George5683/GatorGrid-Mesh/docs/html/ap__one_8cpp__incl.png

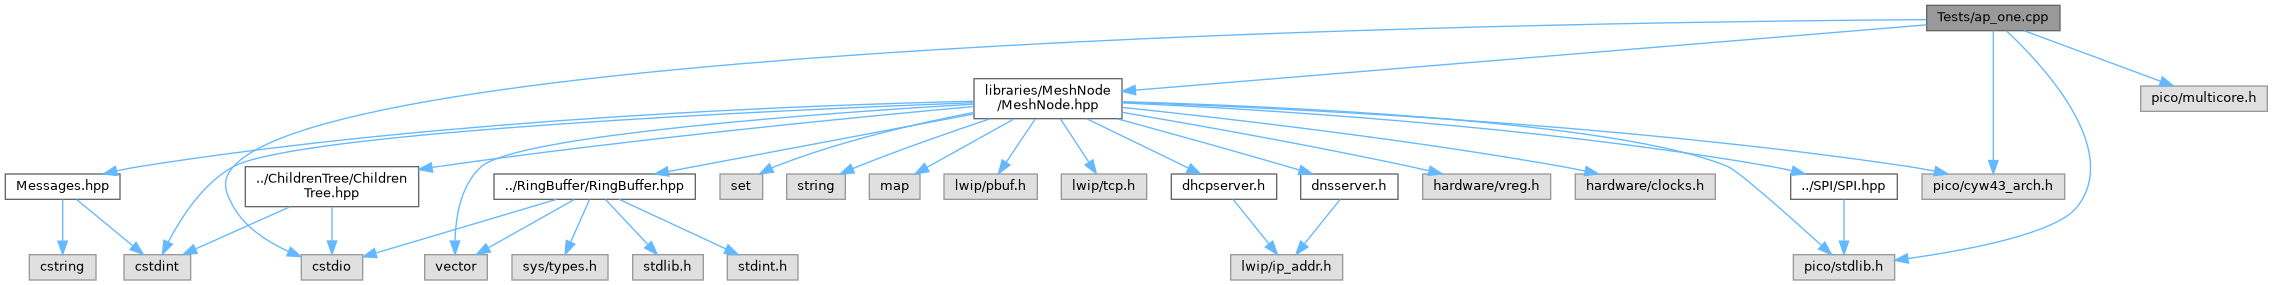
docs/html/ap__one_8cpp__incl.png
