George5683/GatorGrid-Mesh/docs/html/ChildrenTree_8cpp__incl.png

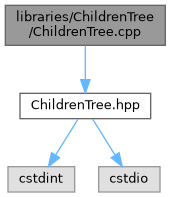
docs/html/ChildrenTree_8cpp__incl.png
