George5683/GatorGrid-Mesh/docs/html/ChildrenTree_8hpp__dep__incl.png

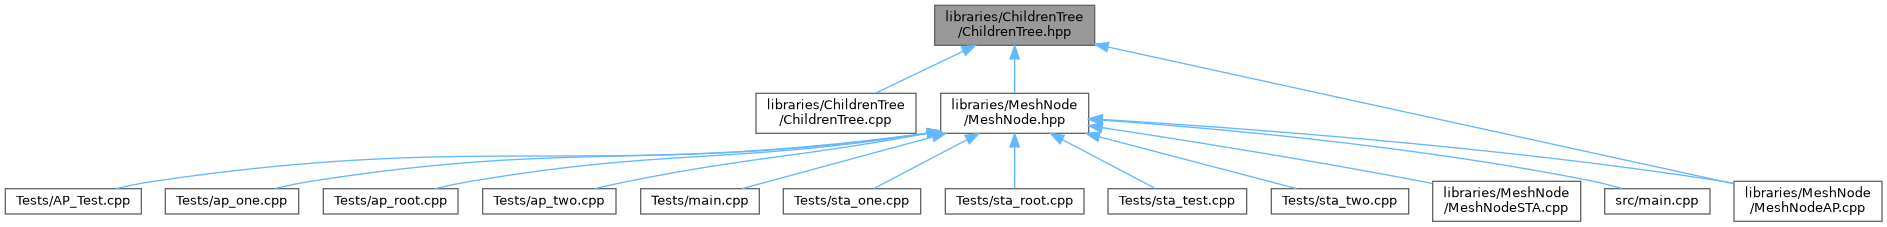
docs/html/ChildrenTree_8hpp__dep__incl.png
