George5683/GatorGrid-Mesh/docs/html/classAPNode__coll__graph.png

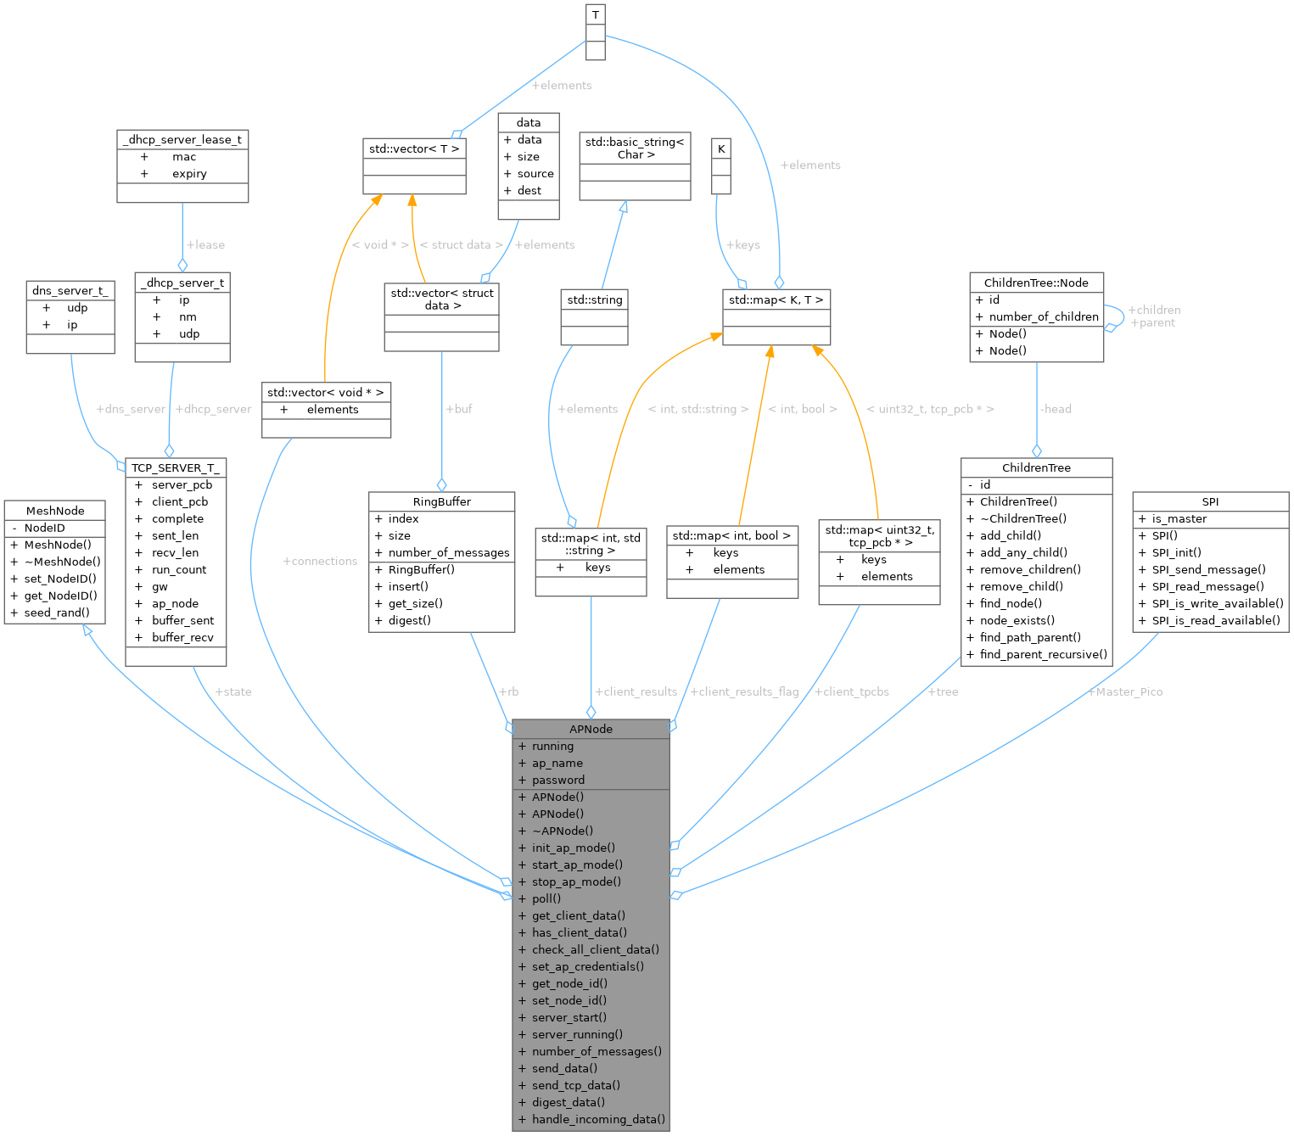
docs/html/classAPNode__coll__graph.png
