George5683/GatorGrid-Mesh/docs/html/classChildrenTree__coll__graph.png

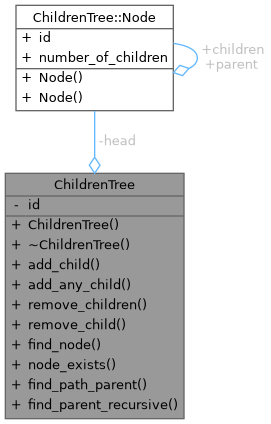
docs/html/classChildrenTree__coll__graph.png
