George5683/GatorGrid-Mesh/docs/html/classMeshNode__coll__graph.png

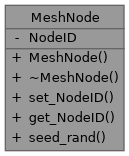
docs/html/classMeshNode__coll__graph.png
