George5683/GatorGrid-Mesh/docs/html/classMeshNode__inherit__graph.png

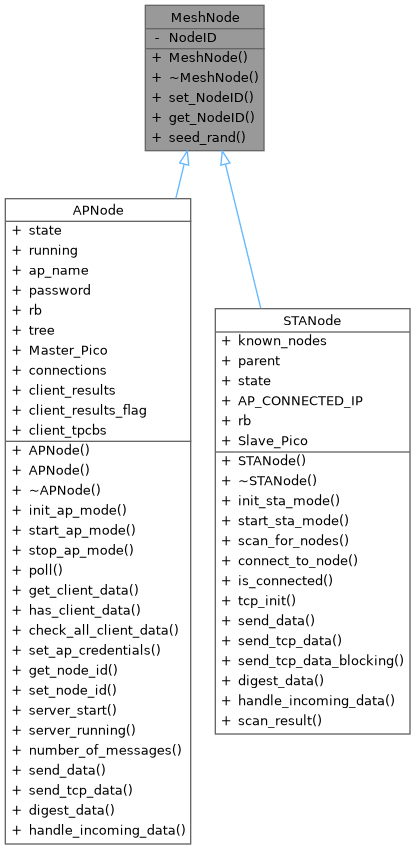
docs/html/classMeshNode__inherit__graph.png
