George5683/GatorGrid-Mesh/docs/html/classRingBuffer__coll__graph.png

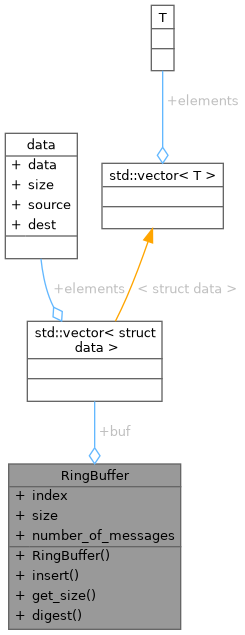
docs/html/classRingBuffer__coll__graph.png
