George5683/GatorGrid-Mesh/docs/html/classSPI__coll__graph.png

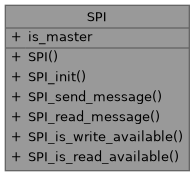
docs/html/classSPI__coll__graph.png
