George5683/GatorGrid-Mesh/docs/html/classSTANode__coll__graph.png

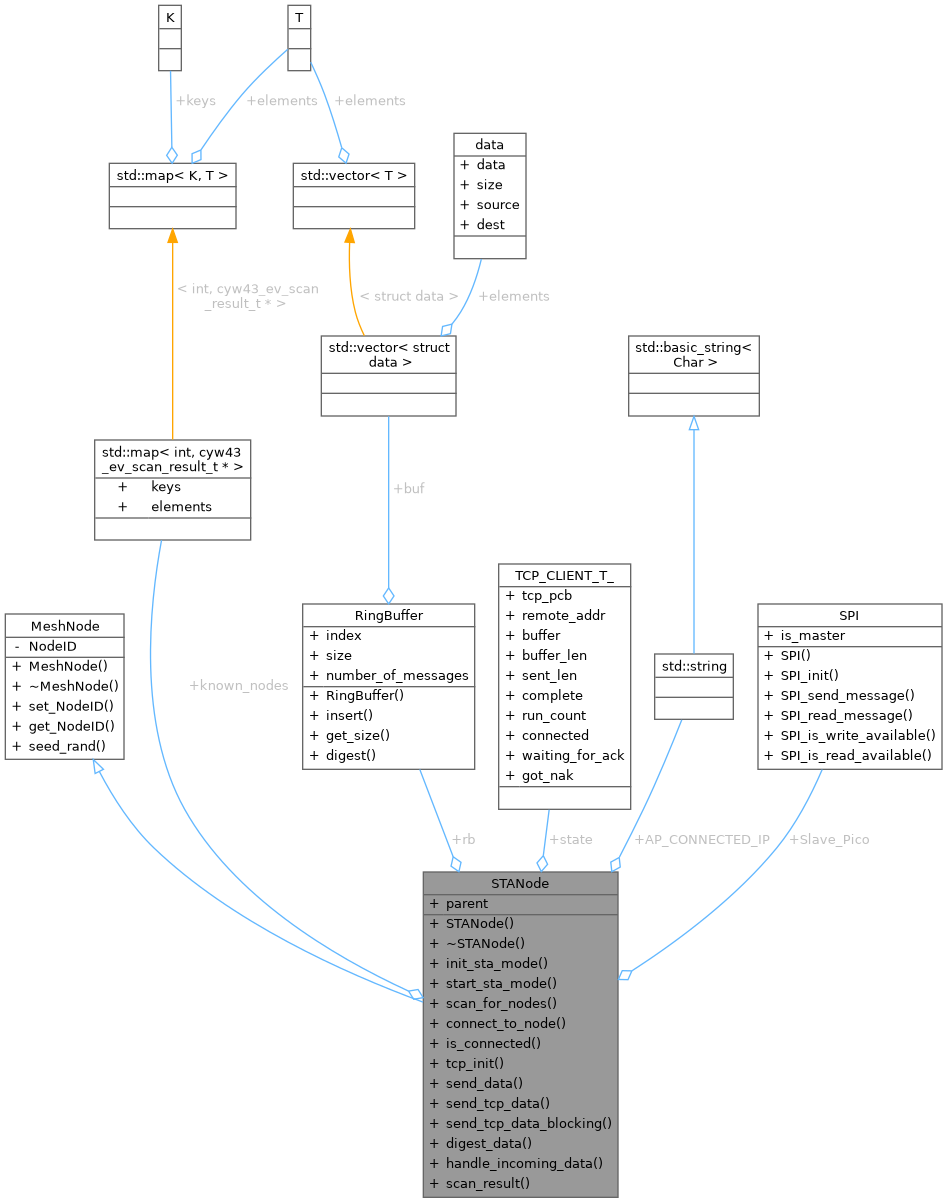
docs/html/classSTANode__coll__graph.png
