George5683/GatorGrid-Mesh/docs/html/classSTANode__inherit__graph.png

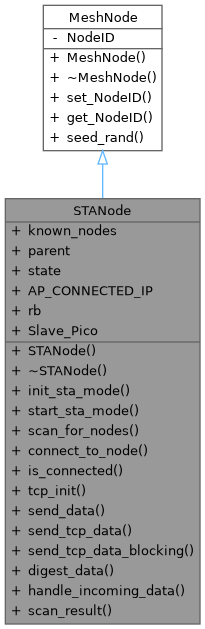
docs/html/classSTANode__inherit__graph.png
