George5683/GatorGrid-Mesh/docs/html/classTCP__ACK__MESSAGE__coll__graph.png

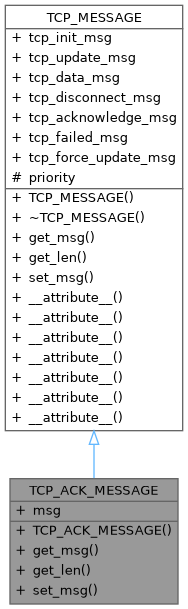
docs/html/classTCP__ACK__MESSAGE__coll__graph.png
