George5683/GatorGrid-Mesh/docs/html/classTCP__DATA__MSG__coll__graph.png

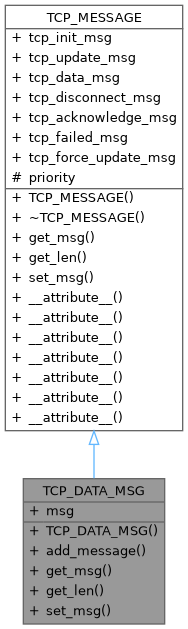
docs/html/classTCP__DATA__MSG__coll__graph.png
