George5683/GatorGrid-Mesh/docs/html/classTCP__MESSAGE__coll__graph.png

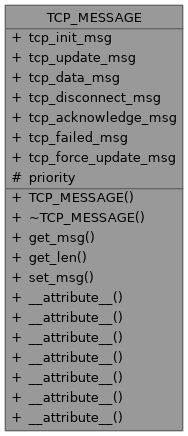
docs/html/classTCP__MESSAGE__coll__graph.png
