George5683/GatorGrid-Mesh/docs/html/classTCP__MESSAGE__inherit__graph.png

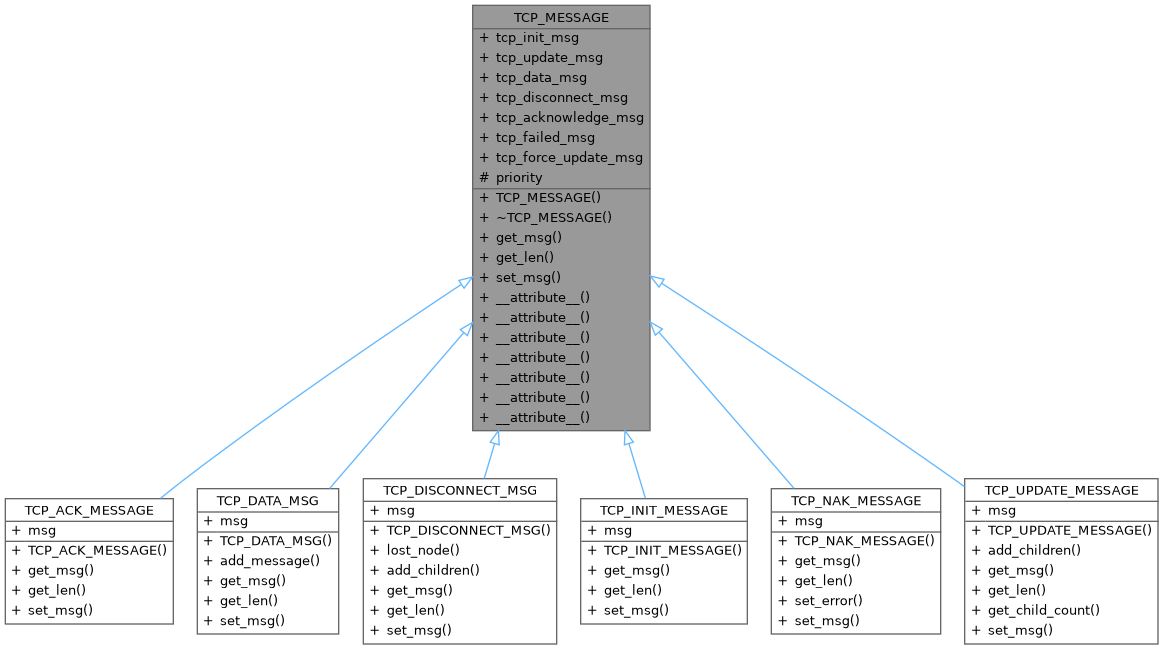
docs/html/classTCP__MESSAGE__inherit__graph.png
