George5683/GatorGrid-Mesh/docs/html/classTCP__NAK__MESSAGE__coll__graph.png

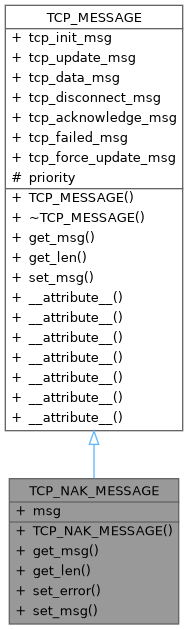
docs/html/classTCP__NAK__MESSAGE__coll__graph.png
