George5683/GatorGrid-Mesh/docs/html/dhcpserver_8c__incl.png

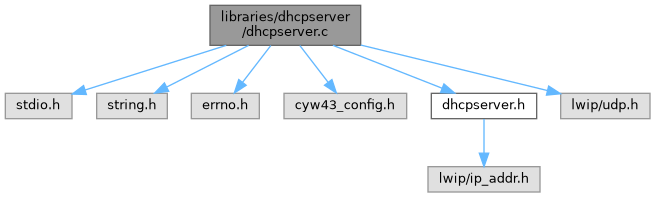
docs/html/dhcpserver_8c__incl.png
