George5683/GatorGrid-Mesh/docs/html/dhcpserver_8h__dep__incl.png

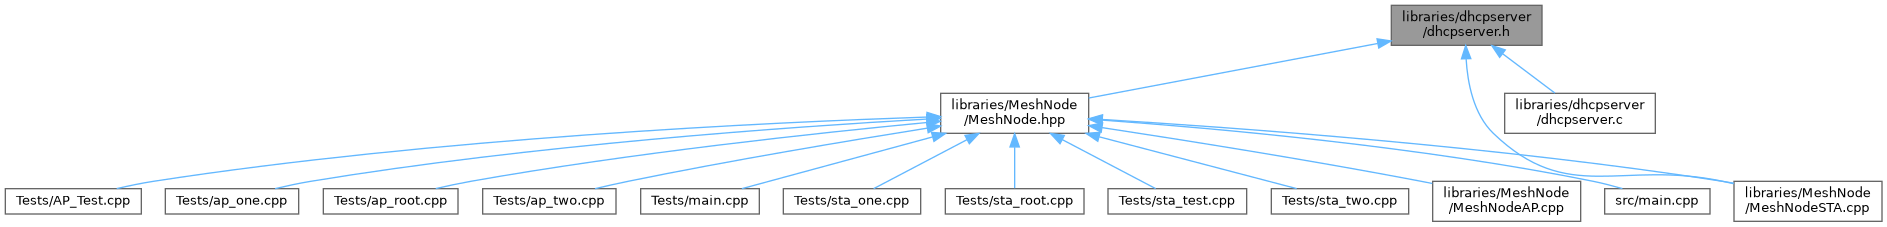
docs/html/dhcpserver_8h__dep__incl.png
