George5683/GatorGrid-Mesh/docs/html/dir_33c78a012c8d08979f57a54a07694c46_dep.png

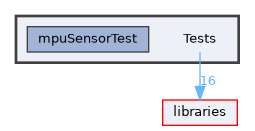
docs/html/dir_33c78a012c8d08979f57a54a07694c46_dep.png
