George5683/GatorGrid-Mesh/docs/html/dir_bc0718b08fb2015b8e59c47b2805f60c_dep.png

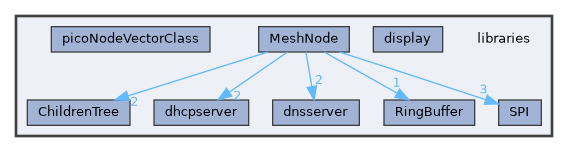
docs/html/dir_bc0718b08fb2015b8e59c47b2805f60c_dep.png
