George5683/GatorGrid-Mesh/docs/html/dir_e2eb97f4390ebb17dad96716298a140a_dep.png

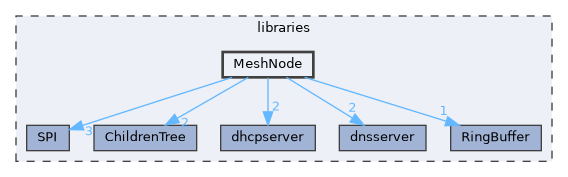
docs/html/dir_e2eb97f4390ebb17dad96716298a140a_dep.png
