George5683/GatorGrid-Mesh/docs/html/dnsserver_8c__incl.png

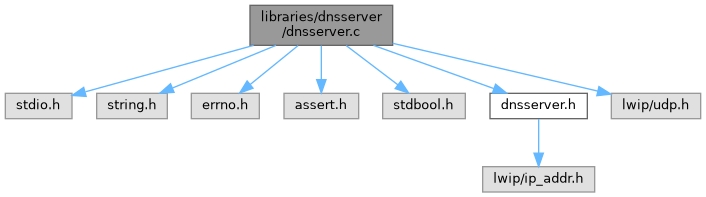
docs/html/dnsserver_8c__incl.png
