George5683/GatorGrid-Mesh/docs/html/dnsserver_8h__incl.png

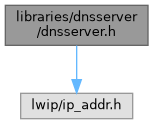
docs/html/dnsserver_8h__incl.png
