George5683/GatorGrid-Mesh/docs/html/inherit_graph_15.png

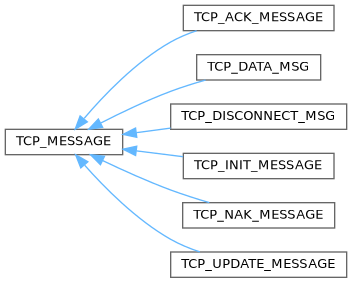
docs/html/inherit_graph_15.png
