George5683/GatorGrid-Mesh/docs/html/MeshNode_8hpp__incl.png

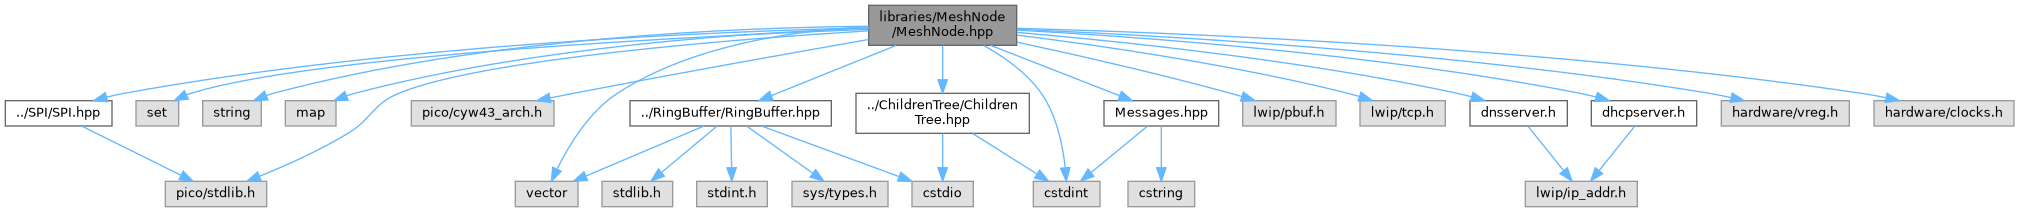
docs/html/MeshNode_8hpp__incl.png
