George5683/GatorGrid-Mesh/docs/html/MeshNodeAP_8cpp__incl.png

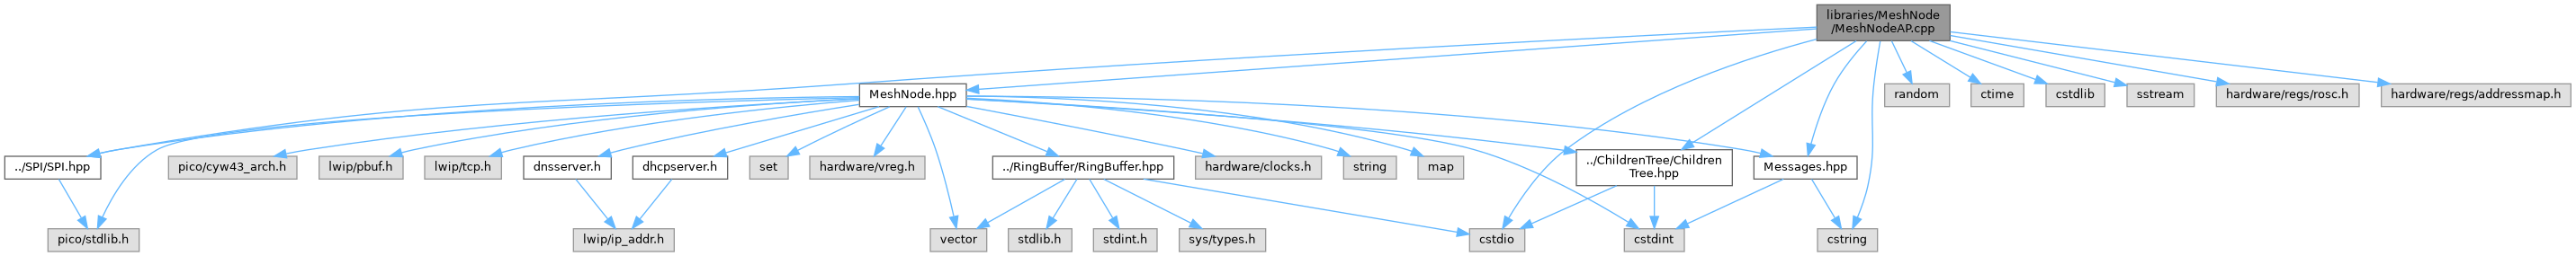
docs/html/MeshNodeAP_8cpp__incl.png
