George5683/GatorGrid-Mesh/docs/html/MeshNodeSTA_8cpp__incl.png

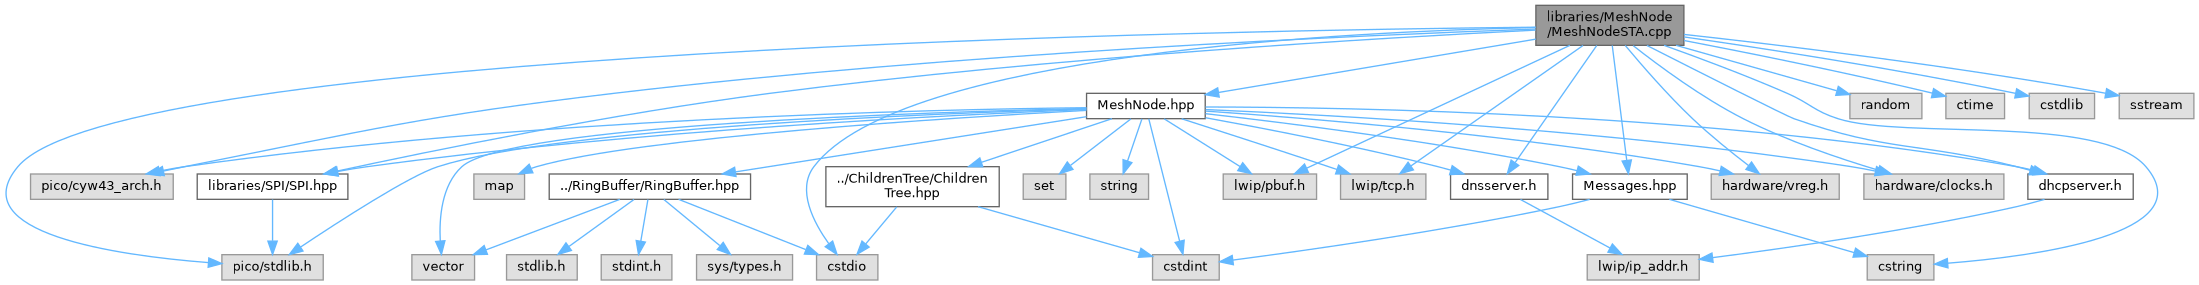
docs/html/MeshNodeSTA_8cpp__incl.png
