George5683/GatorGrid-Mesh/docs/html/Messages_8cpp__incl.png

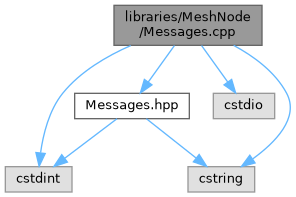
docs/html/Messages_8cpp__incl.png
