George5683/GatorGrid-Mesh/docs/html/Messages_8hpp__incl.png

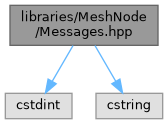
docs/html/Messages_8hpp__incl.png
