George5683/GatorGrid-Mesh/docs/html/RingBuffer_8cpp__incl.png

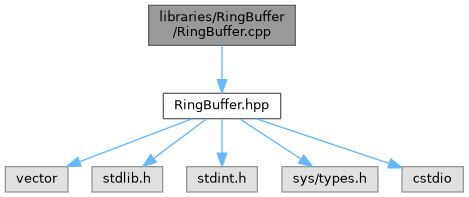
docs/html/RingBuffer_8cpp__incl.png
