George5683/GatorGrid-Mesh/docs/html/RingBuffer_8hpp__incl.png

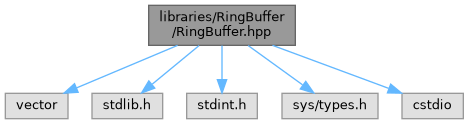
docs/html/RingBuffer_8hpp__incl.png
