George5683/GatorGrid-Mesh/docs/html/SPI_8cpp__incl.png

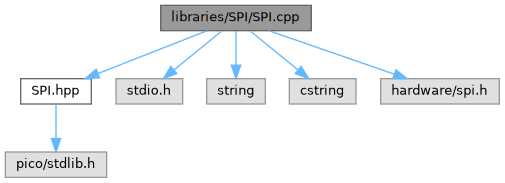
docs/html/SPI_8cpp__incl.png
