George5683/GatorGrid-Mesh/docs/html/SPI_8hpp__dep__incl.png

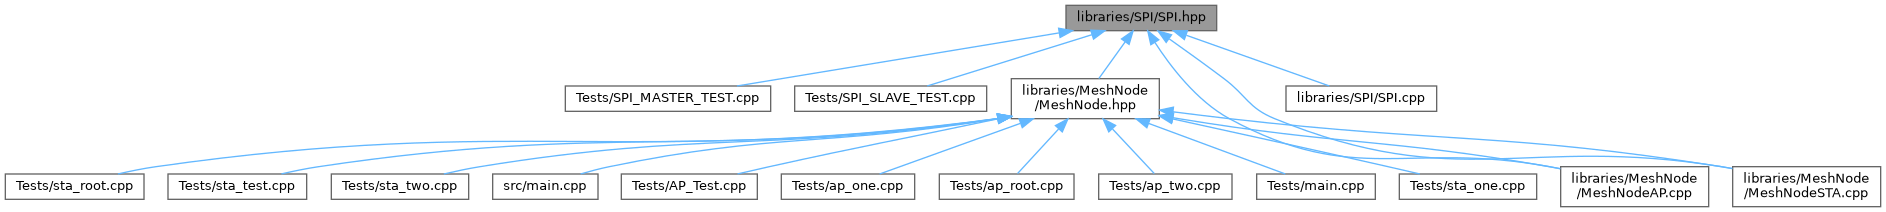
docs/html/SPI_8hpp__dep__incl.png
