George5683/GatorGrid-Mesh/docs/html/src_2main_8cpp__incl.png

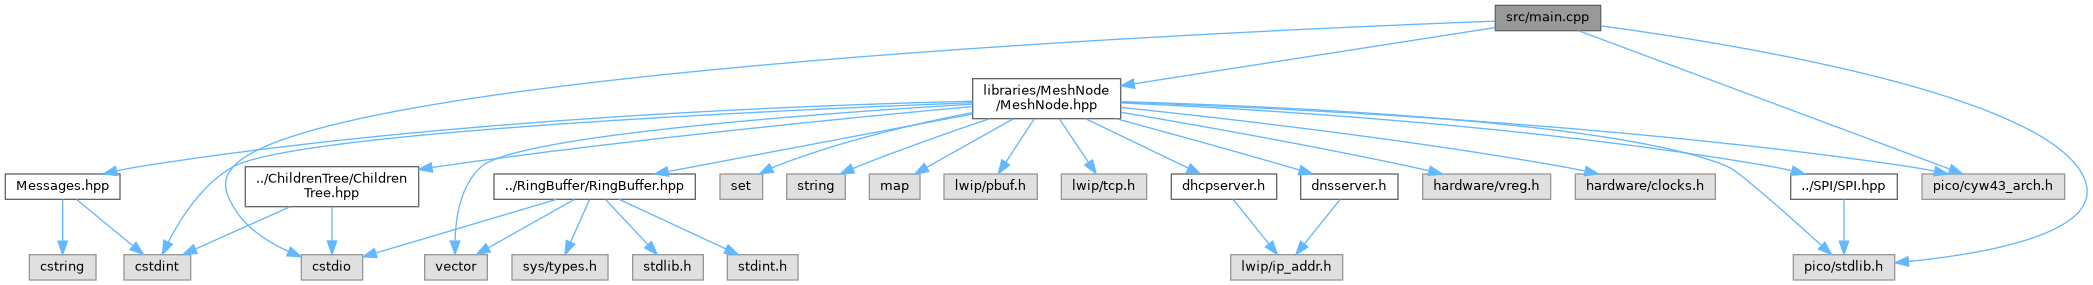
docs/html/src_2main_8cpp__incl.png
