George5683/GatorGrid-Mesh/docs/html/sta__two_8cpp__incl.png

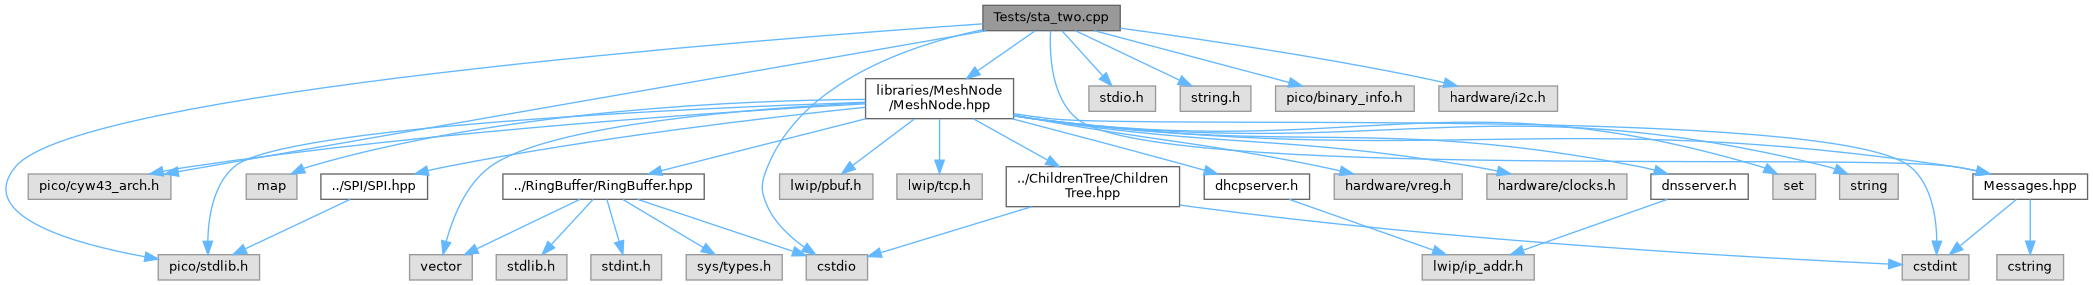
docs/html/sta__two_8cpp__incl.png
