George5683/GatorGrid-Mesh/docs/html/struct__dhcp__server__t__coll__graph.png

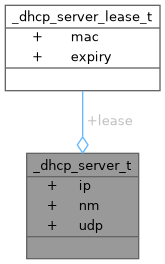
docs/html/struct__dhcp__server__t__coll__graph.png
