George5683/GatorGrid-Mesh/docs/html/structdns__header__t____coll__graph.png

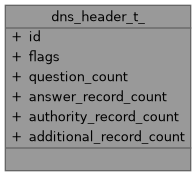
docs/html/structdns__header__t____coll__graph.png
