George5683/GatorGrid-Mesh/docs/html/structTCP__CONNECT__STATE__T____coll__graph.png

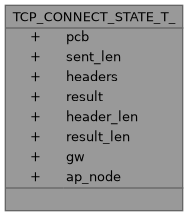
docs/html/structTCP__CONNECT__STATE__T____coll__graph.png
