George5683/GatorGrid-Mesh/docs/html/AP__Test_8cpp__incl.png

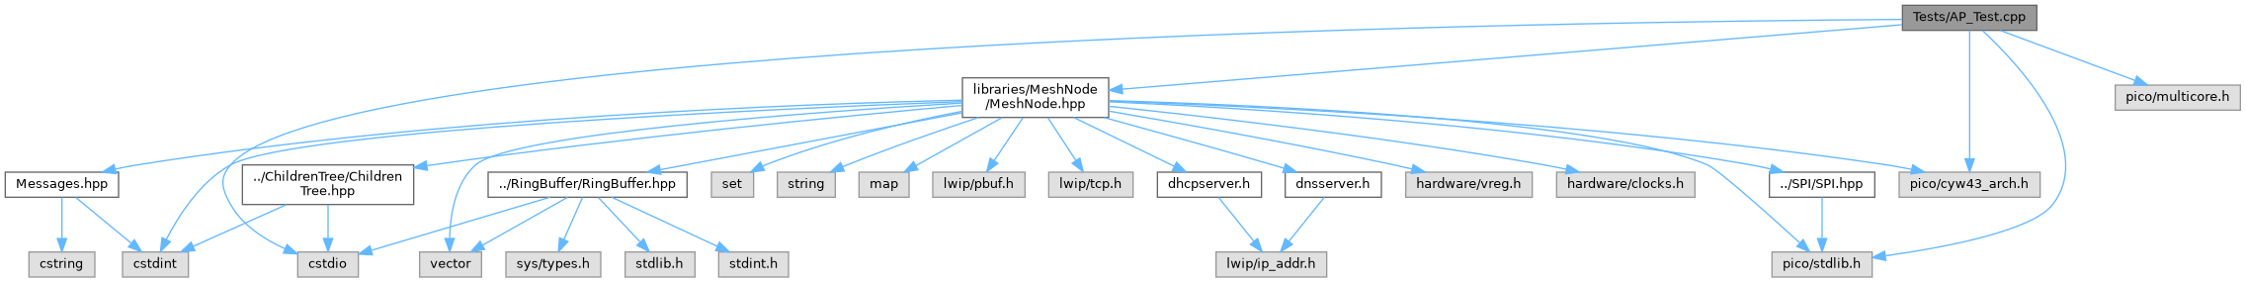
docs/html/AP__Test_8cpp__incl.png
