George5683/GatorGrid-Mesh/Tests/ap_one.cpp

#include "pico/stdlib.h"
#include "libraries/MeshNode/MeshNode.hpp"
#include <cstdio>
#include "pico/cyw43_arch.h"
#include "pico/multicore.h"


bool is_wifi_connected = false;
#define DEBUG 1

int main() {

    // initiate everything
    stdio_init_all();

    APNode node(1);

    sleep_ms(5000);

    //PicoUART uart;

    /*cyw43_arch_init();

    printf("starting uart\n");
    uart.picoUARTInit();
    printf("uart  nitalized\n");
    uart.picoUARTInterruptInit();
    printf("uart intterupts initalized\n");

    printf("Init totally finished\n");*/

    /*while(true) {
        printf("ping\n");
        cyw43_arch_gpio_put(CYW43_WL_GPIO_LED_PIN, true);
        sleep_ms(1000);
        cyw43_arch_gpio_put(CYW43_WL_GPIO_LED_PIN, false);
        sleep_ms(1000);
    }*/

    // initial delay to allow user to look at the serial monitor
    //sleep_ms(5000);

    //multicore_launch_core1(core1_entry);
    

    printf("Init AP Mode\n");
    if (!node.init_ap_mode())
    {
        sleep_ms(1000);
    }

    printf("Starting AP Mode\n");
    if (!node.start_ap_mode()) {
        sleep_ms(1000);
    }

    printf("AP ID: %08x\n", node.get_NodeID());

    
    // if(spi.SPI_send_message(id, 4) != 1) {
    //     for (;;) { sleep_ms(1000); }
    // }
    bool toggle = true;
    int count = 0;

    uint32_t children_ids[4] = {};
    uint8_t number_of_children = 0;
    
    while (node.server_running()) {

        node.poll();

        if (count++ >= 500) {
            cyw43_arch_gpio_put(CYW43_WL_GPIO_LED_PIN, toggle);
            toggle = !toggle;

            node.tree.get_children(node.get_NodeID(), children_ids, number_of_children);
            printf("\n\nChildren:\n");
            for (int i = 0; i < number_of_children; i++) {
                printf("%u\t", children_ids[i]);
            }
            printf("\n");

            count = 0;
        }

        sleep_ms(1);
    }


    for (;;) {
        puts("Exited");
        sleep_ms(1000);
    }
        
    

    return 0;
}
